cbm-instructions/moon-moon/code/arduino/HistoryState.h

#ifndef HISTORY_STATE_H
#define HISTORY_STATE_H

#include <Arduino.h>
#include "State.h"

class HistoryState : public State {
  
    public:
        void setup();
        void loop();
            
};

#endif
