cbm-instructions/moon-moon/code/arduino/RateState.h

//
// Created by Adrian Endrich on 15.01.18.
//

#ifndef ARDUINO_RATESTATE_H
#define ARDUINO_RATESTATE_H


#include "State.h"
#include <Arduino.h>

class RateState : public State{


public:
    void setup();

    void loop();

};


#endif //ARDUINO_RATESTATE_H
