cbm-instructions/moon-moon/code/arduino/SleepingTimeState.h

#ifndef SLEEPING_TIME_STATE_H
#define SLEEPING_TIME_STATE_H

#include <Arduino.h>
#include "State.h"

class SleepingTimeState : public State {
  
    public:
        void setup();
        void loop();
            
};

#endif
